Phila-H-23/AUV-Phytoplankton-Project/Housing Design/housing_sys_arch.png

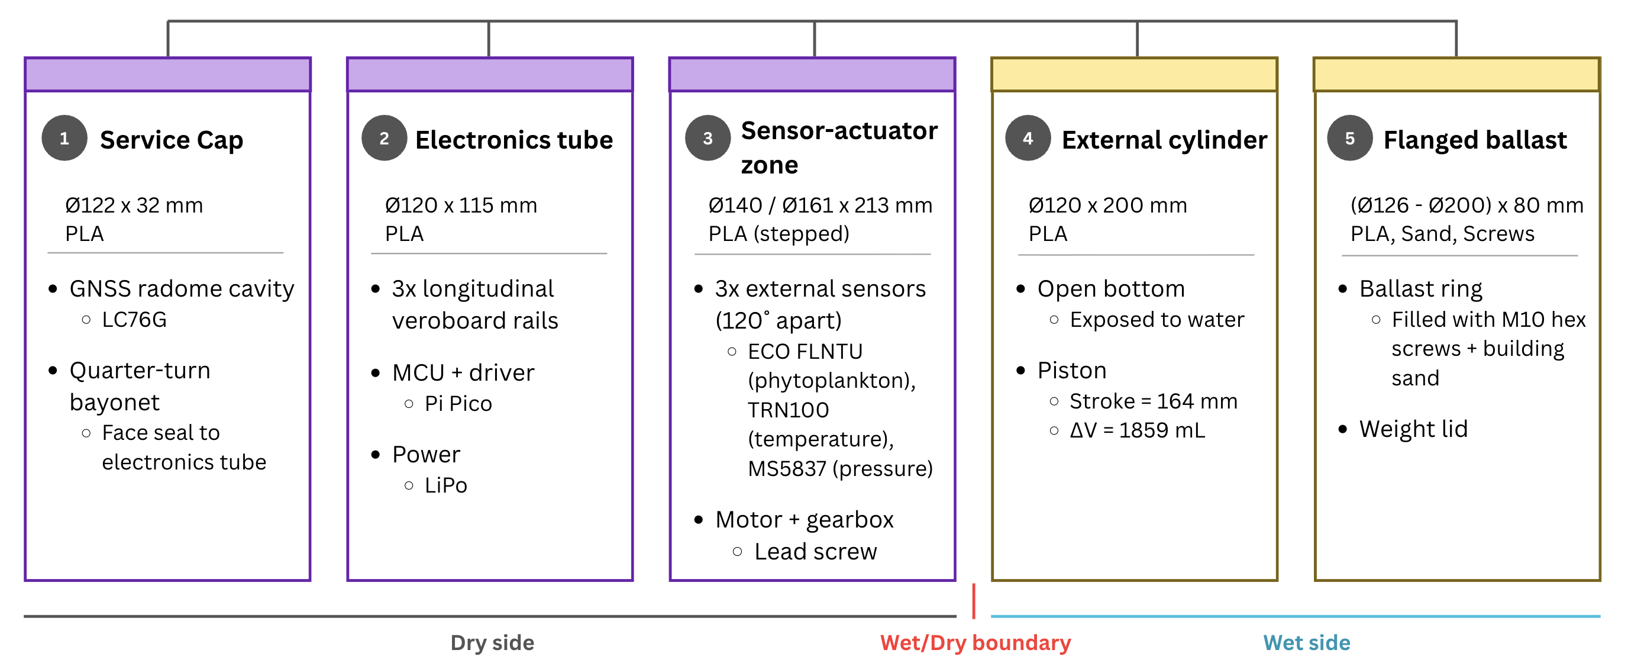
Housing Design/housing_sys_arch.png
