Phila-H-23/AUV-Phytoplankton-Project/Housing Design/renders/electronics_zone.png

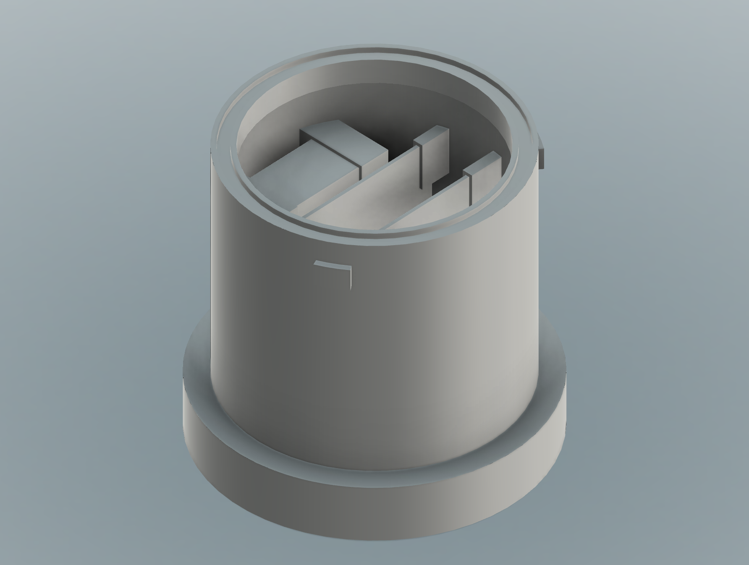
Housing Design/renders/electronics_zone.png
