Phila-H-23/AUV-Phytoplankton-Project/Housing Design/renders/electronics_zone_section.png

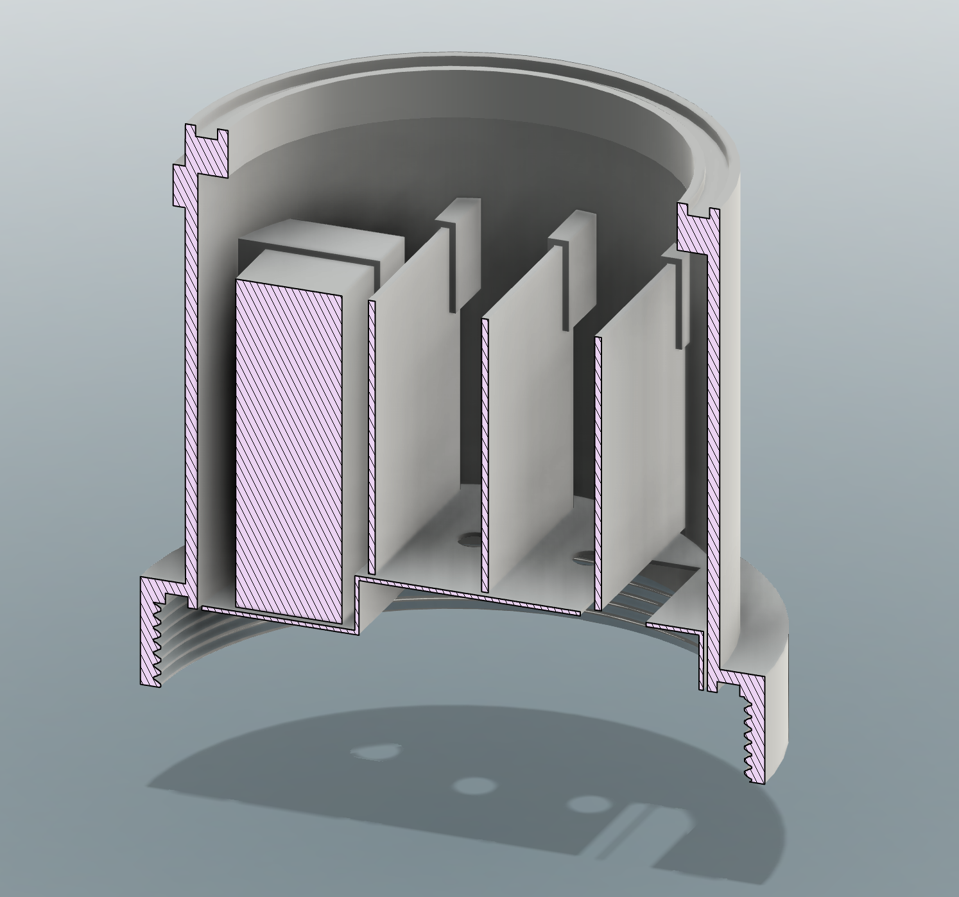
Housing Design/renders/electronics_zone_section.png
