Phila-H-23/AUV-Phytoplankton-Project/Housing Design/renders/sensor_actuator_zone.png

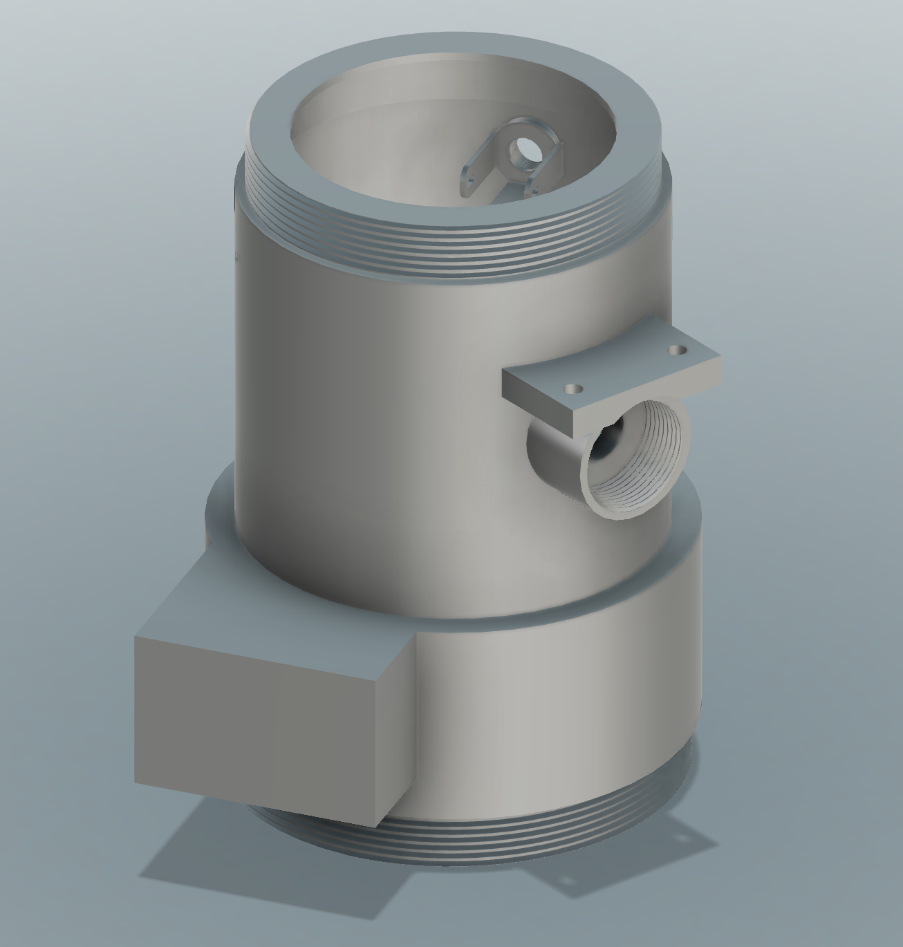
Housing Design/renders/sensor_actuator_zone.png
