Phila-H-23/AUV-Phytoplankton-Project/Housing Design/renders/sensor_actuator_zone_section.png

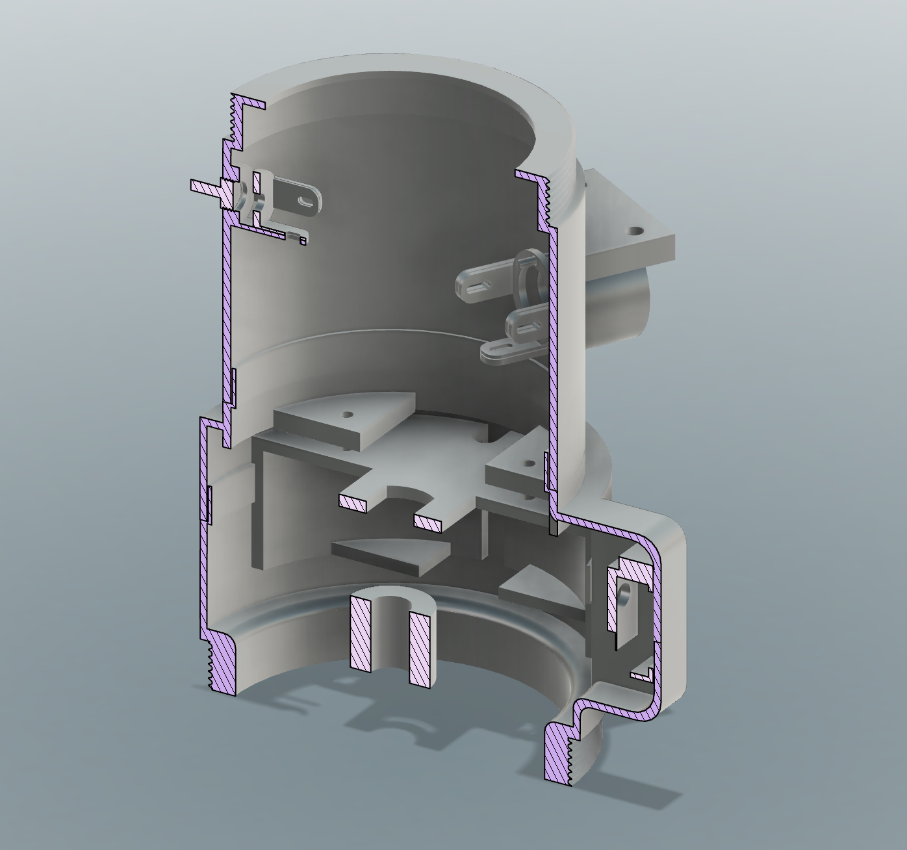
Housing Design/renders/sensor_actuator_zone_section.png
