Phila-H-23/AUV-Phytoplankton-Project/Housing Design/renders/top_cap.png

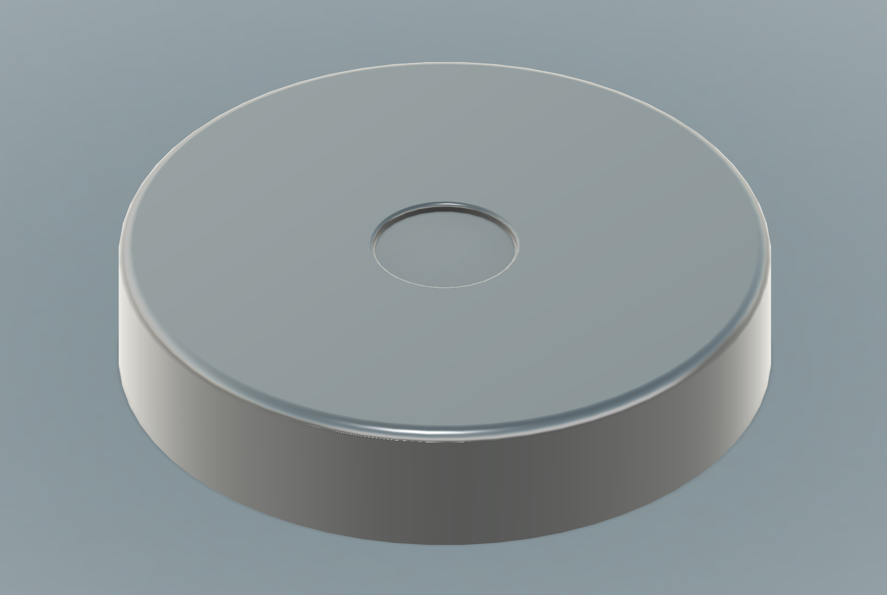
Housing Design/renders/top_cap.png
