Phila-H-23/AUV-Phytoplankton-Project/Housing Design/simulations - simscale/electronics_zone_displacement.png

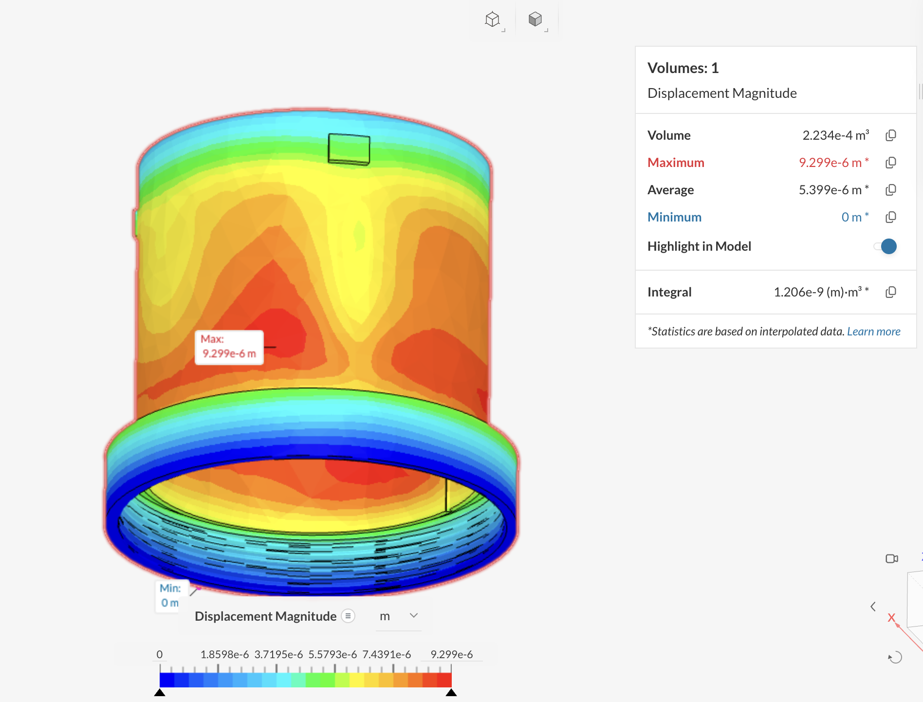
Housing Design/simulations - simscale/electronics_zone_displacement.png
