Phila-H-23/AUV-Phytoplankton-Project/Housing Design/simulations - simscale/electronics_zone_von_mises.png

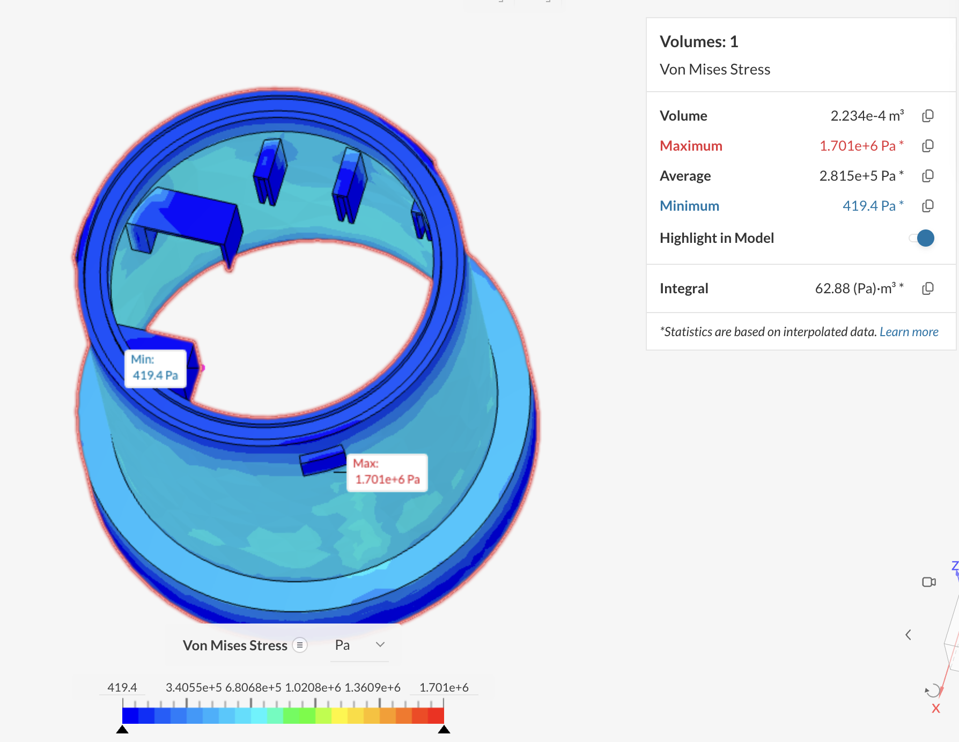
Housing Design/simulations - simscale/electronics_zone_von_mises.png
