Phila-H-23/AUV-Phytoplankton-Project/Housing Design/simulations - simscale/external_cylinder_displacement.png

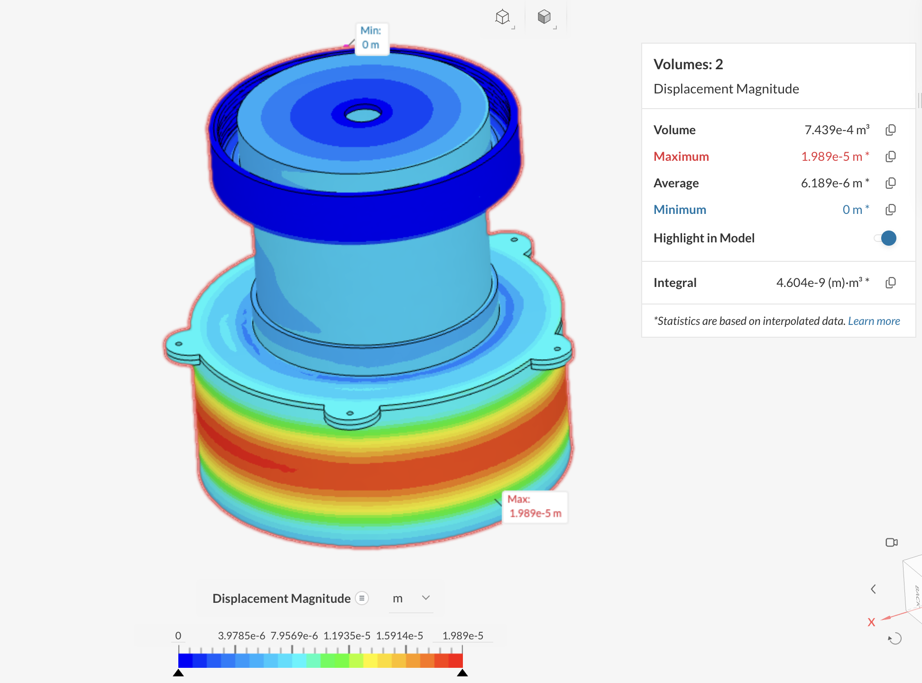
Housing Design/simulations - simscale/external_cylinder_displacement.png
