Phila-H-23/AUV-Phytoplankton-Project/Housing Design/simulations - simscale/external_cylinder_von_mises.png

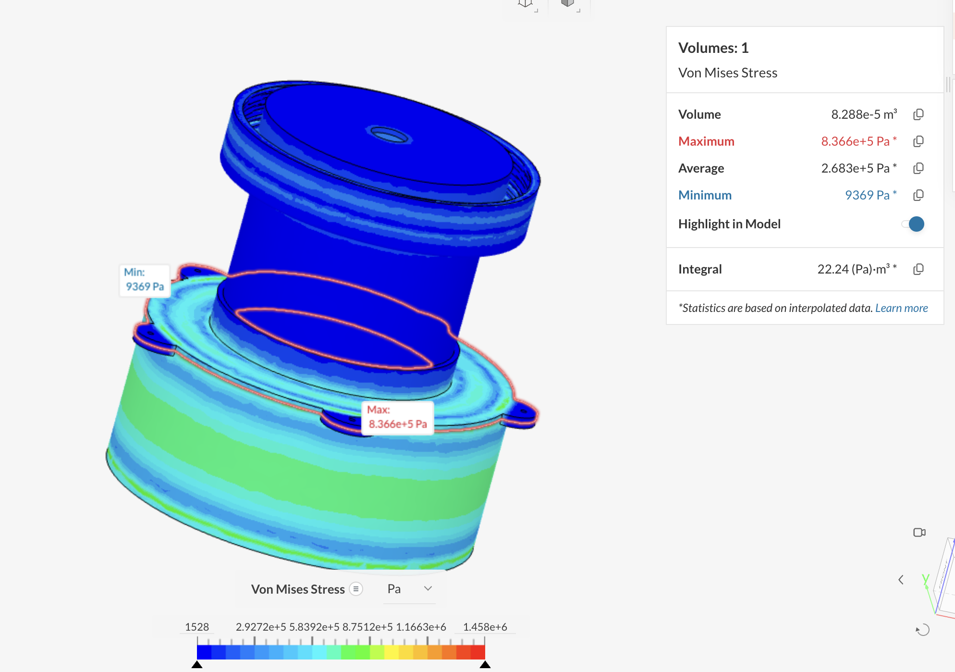
Housing Design/simulations - simscale/external_cylinder_von_mises.png
