Phila-H-23/AUV-Phytoplankton-Project/Housing Design/simulations - simscale/sensor_actuator_displacement.png

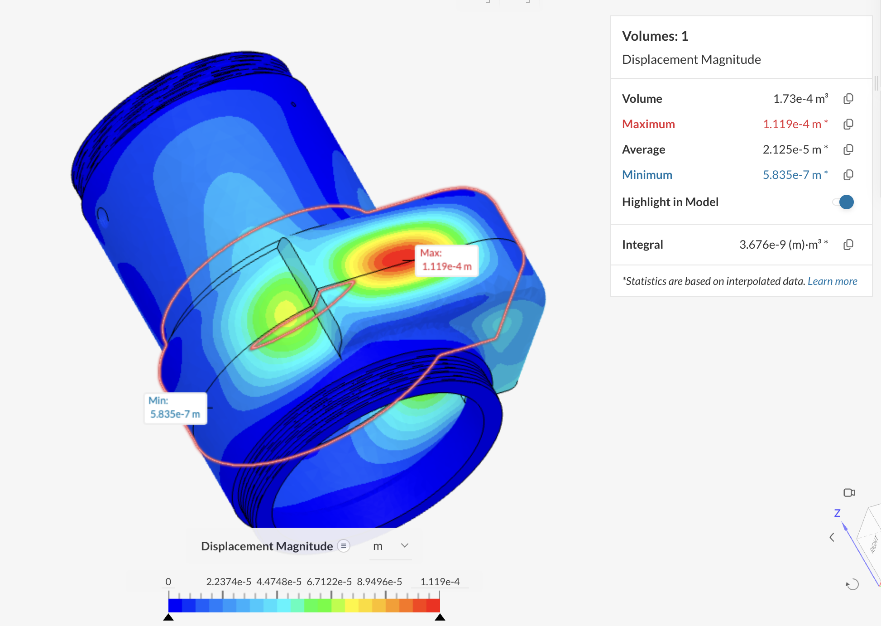
Housing Design/simulations - simscale/sensor_actuator_displacement.png
