Phila-H-23/AUV-Phytoplankton-Project/Housing Design/simulations - simscale/sensor_actuator_von_mises.png

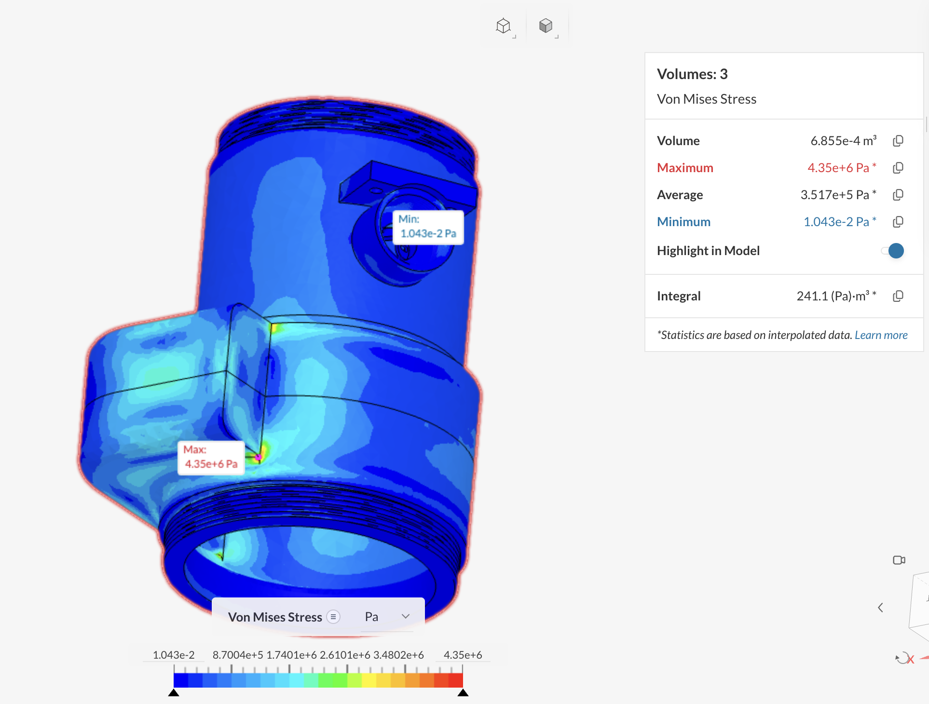
Housing Design/simulations - simscale/sensor_actuator_von_mises.png
