Phila-H-23/AUV-Phytoplankton-Project/Housing Design/weight_calculator_actual.png

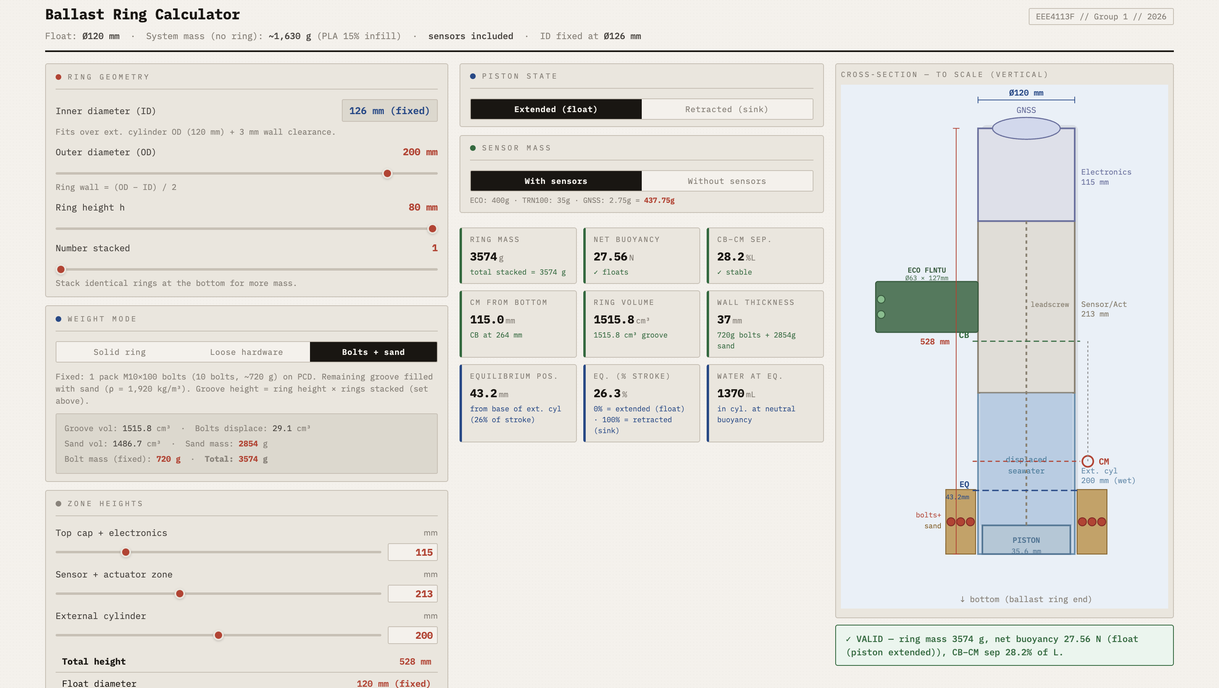
Housing Design/weight_calculator_actual.png
