Phila-H-23/AUV-Phytoplankton-Project/Housing Design/system components - stl files/weight lid - model.stl

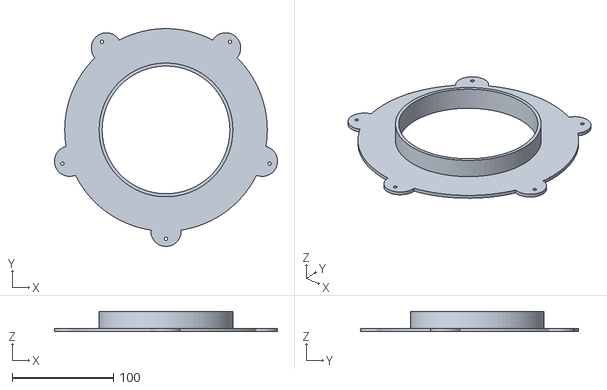
[picture p34: CAD file, 2026-05-17]
Housing Design/system components - stl files/weight lid - model.stl
220.1 x 215.0 x 20.0
