Phila-H-23/AUV-Phytoplankton-Project/Housing Design/system components - stl files/temp sensor fastener - model.stl

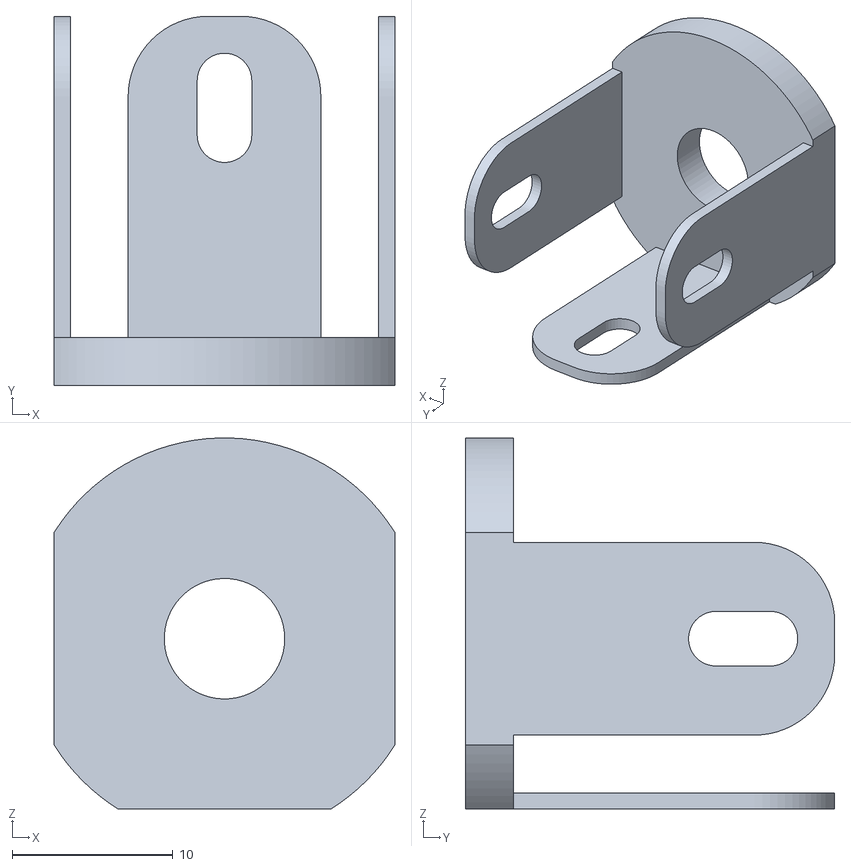
[picture p35: CAD file, 2026-05-17]
Housing Design/system components - stl files/temp sensor fastener - model.stl
21.2 x 23.0 x 23.1
